pzfreo/gib-tuners-mk2/reference/peghead-and-shaft.step

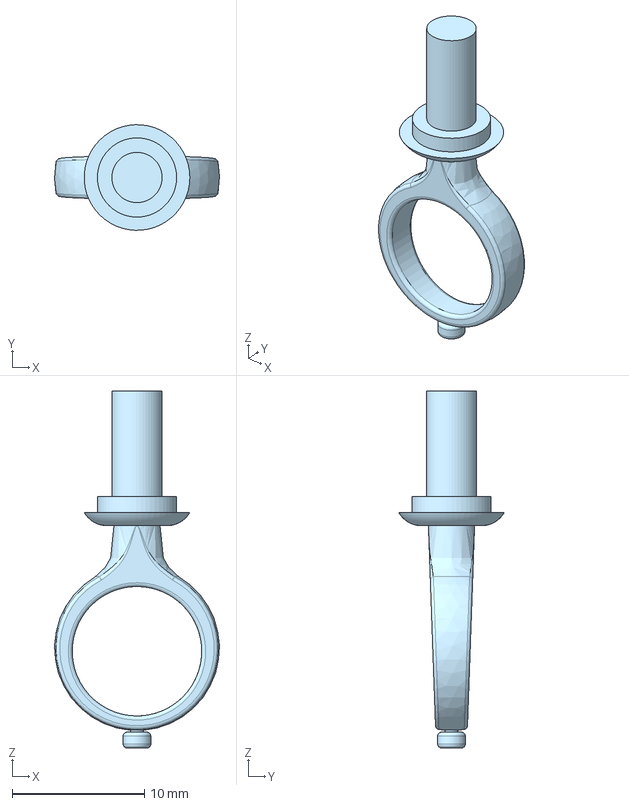
[picture p12: CAD file, 2026-01-29]
reference/peghead-and-shaft.step
12.5 x 8.00 x 27.0 mm
