pzfreo/gib-tuners-mk2/reference/peg.dxf

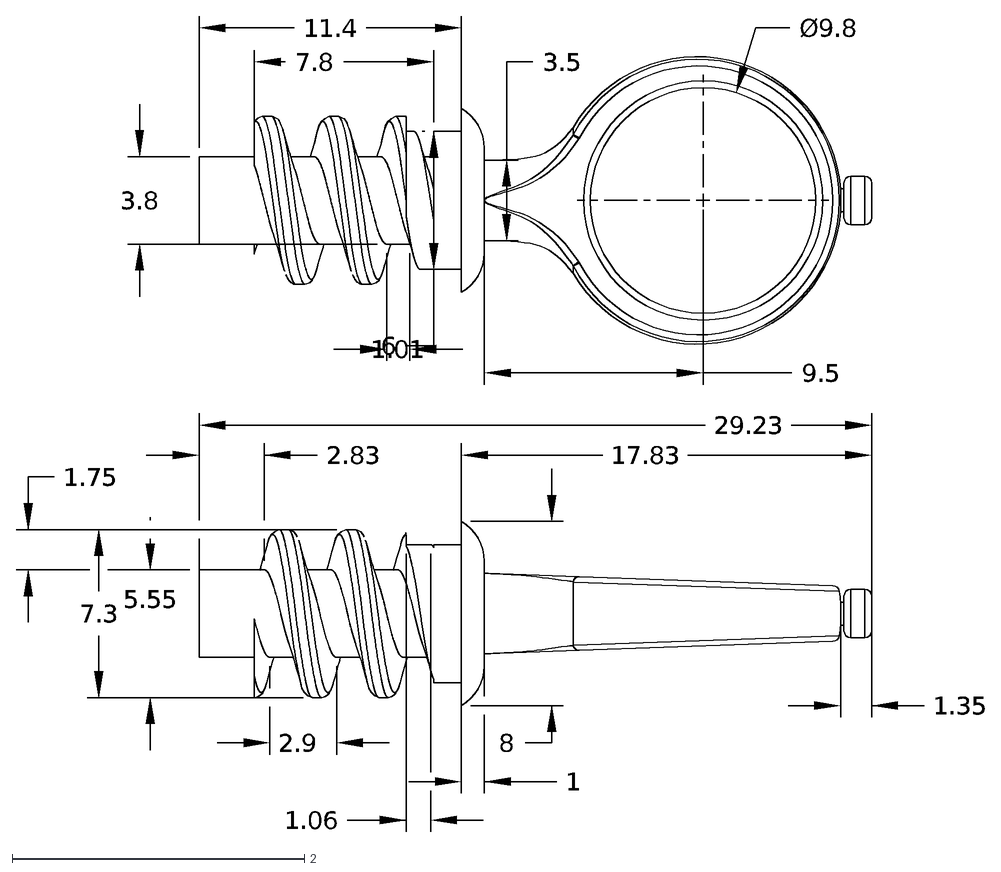
[picture p13: CAD file, 2026-01-29]
reference/peg.dxf
3.5
Ø9.8
3.8
1.01
9.5
7.8
6
7.3
2.9
2.83
1.35
17.83
29.23
8
1
1.06
11.4
5.55
1.75
