pzfreo/gib-tuners-mk2/reference/worm.step

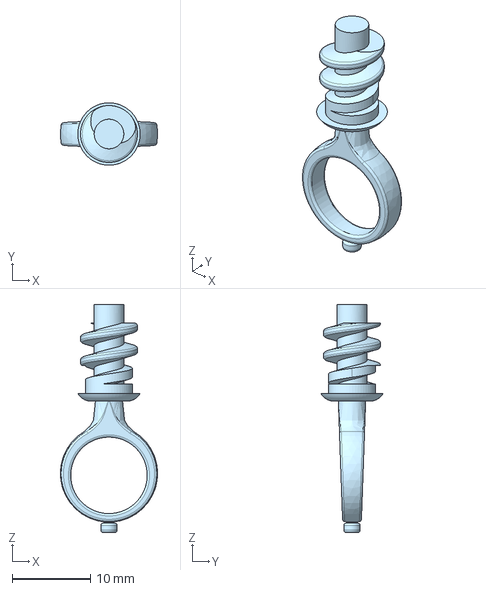
[picture p14: CAD file, 2026-01-29]
reference/worm.step
12.5 x 8.00 x 29.2 mm
