pzfreo/gib-tuners-mk2/sent/ptype/peg_head_lh.step

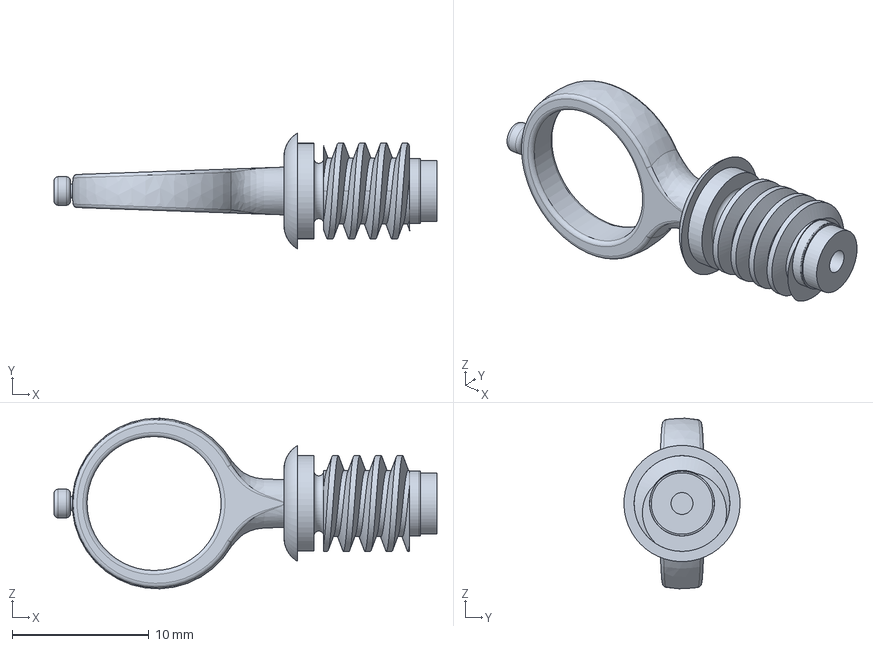
[picture p15: CAD file, 2026-03-25]
sent/ptype/peg_head_lh.step
28.0 x 8.50 x 12.5 mm
