pzfreo/gib-tuners-mk2/reference/rhframe.step

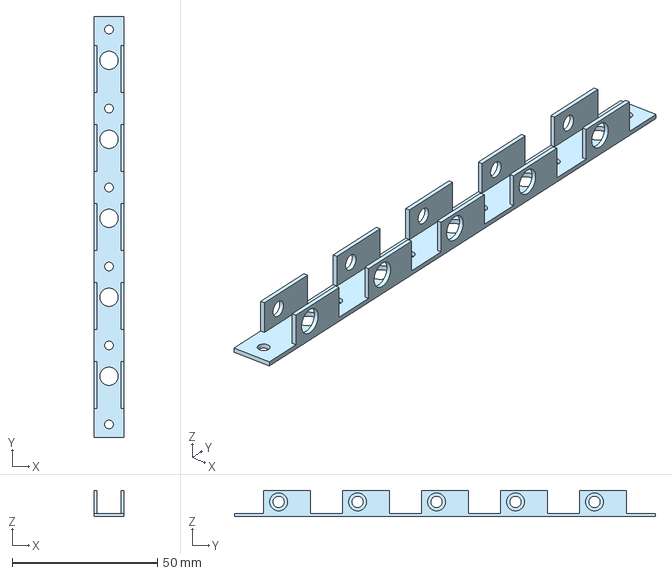
[picture p16: CAD file, 2026-01-29]
reference/rhframe.step
10.3 x 145.0 x 9.00 mm
