pzfreo/gib-tuners-mk2/reference/pegsmall.dxf

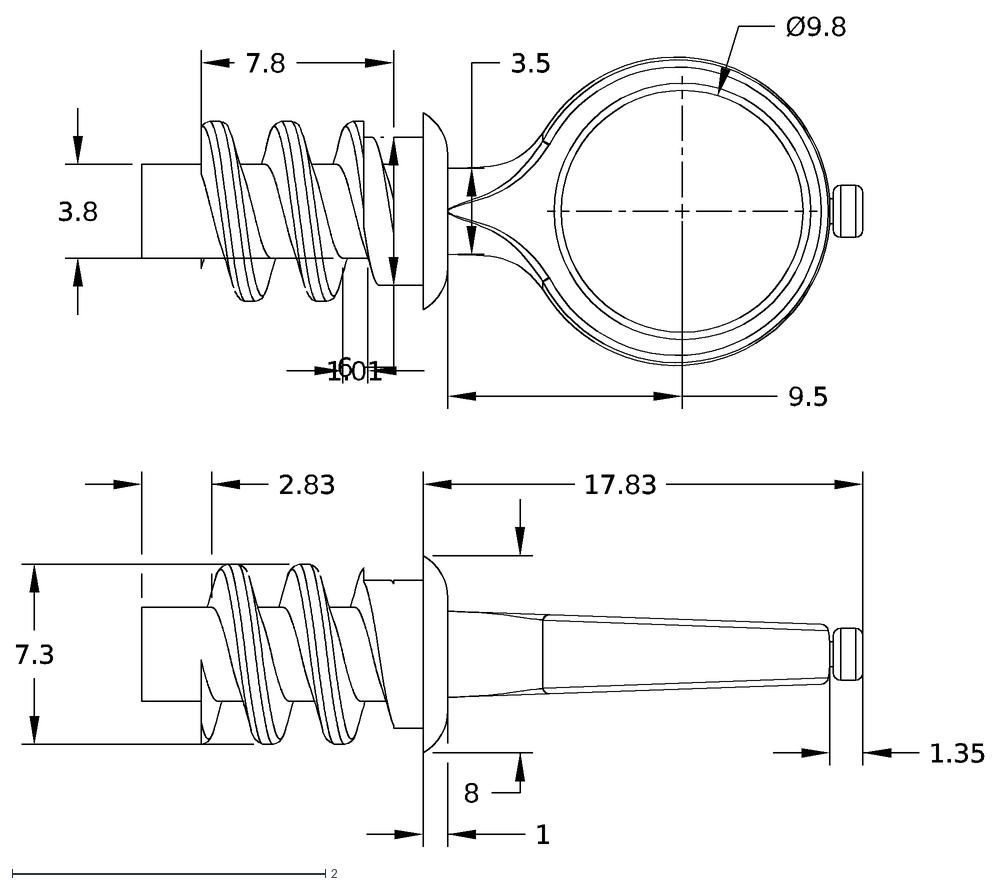
[picture p17: CAD file, 2026-01-29]
reference/pegsmall.dxf
3.5
Ø9.8
3.8
1.01
9.5
7.8
6
7.3
2.83
1.35
17.83
8
1
