pzfreo/gib-tuners-mk2/reference/worm_m0.5_z1.step

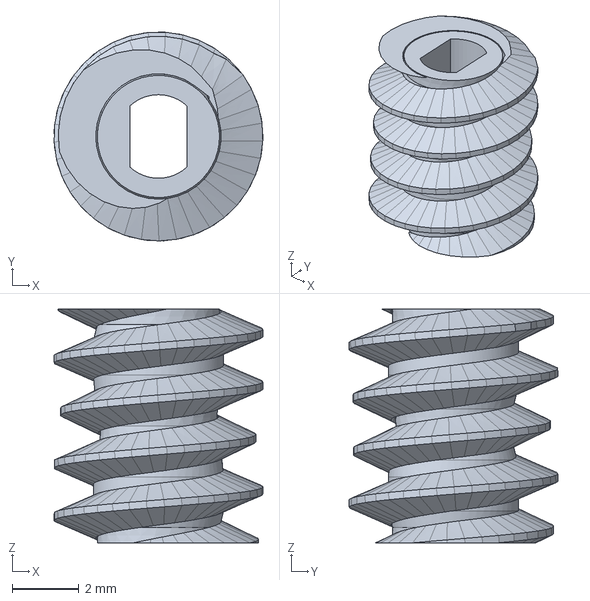
[picture p18: CAD file, 2026-01-28]
reference/worm_m0.5_z1.step
6.25 x 6.25 x 7.00 mm
